criterionsignalworks/ranka/images/ranka-n1-eda-2.png

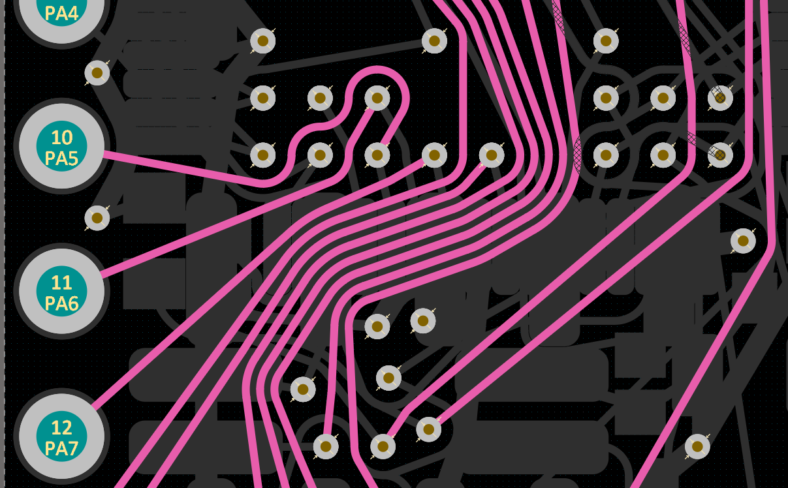
images/ranka-n1-eda-2.png
