criterionsignalworks/ranka/images/ranka-n1-eda-layer-3d.png

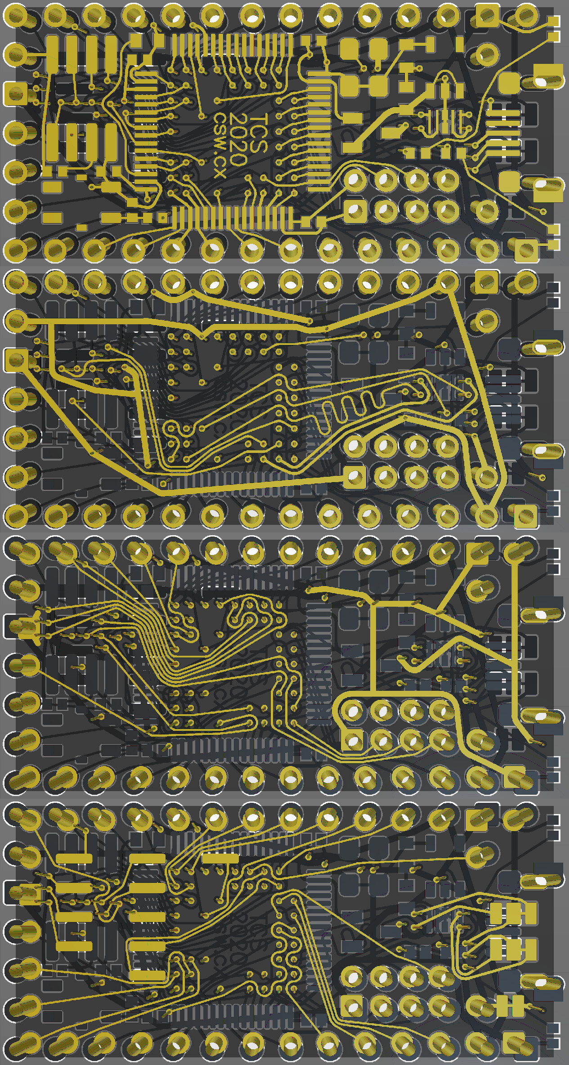
images/ranka-n1-eda-layer-3d.png
