criterionsignalworks/ranka/images/ranka-n1-top-1.jpg

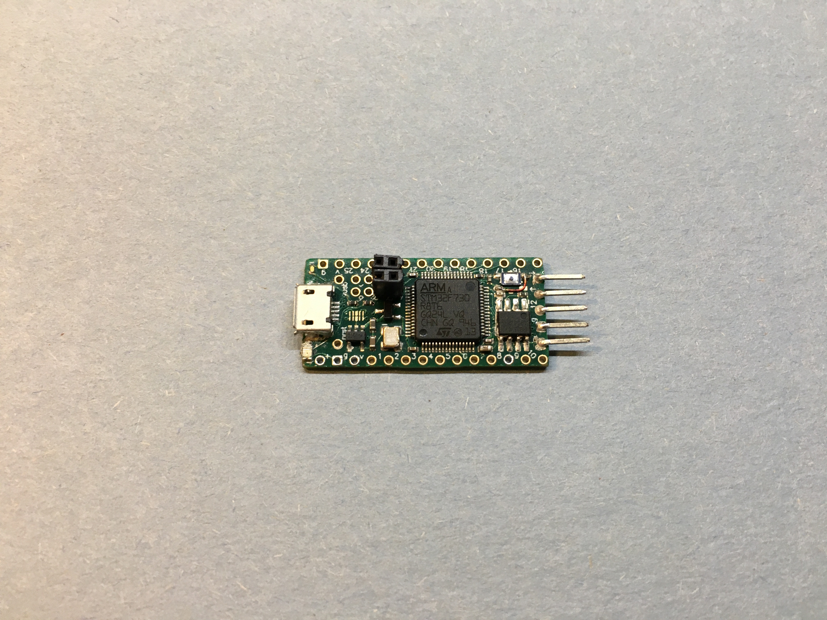
images/ranka-n1-top-1.jpg
