criterionsignalworks/ranka/images/ranka-n1-top-blurry.jpg

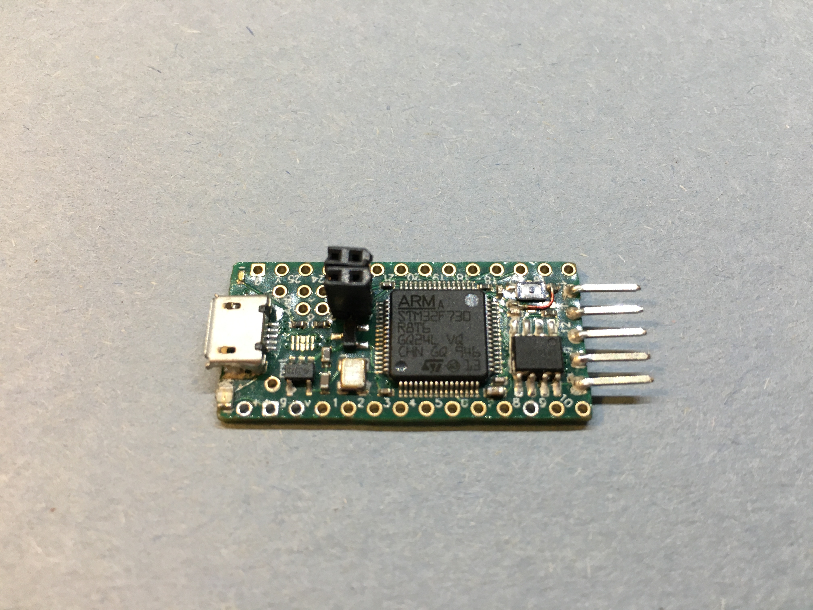
images/ranka-n1-top-blurry.jpg
