criterionsignalworks/ranka/images/tcs-ranka-n0-5.jpg

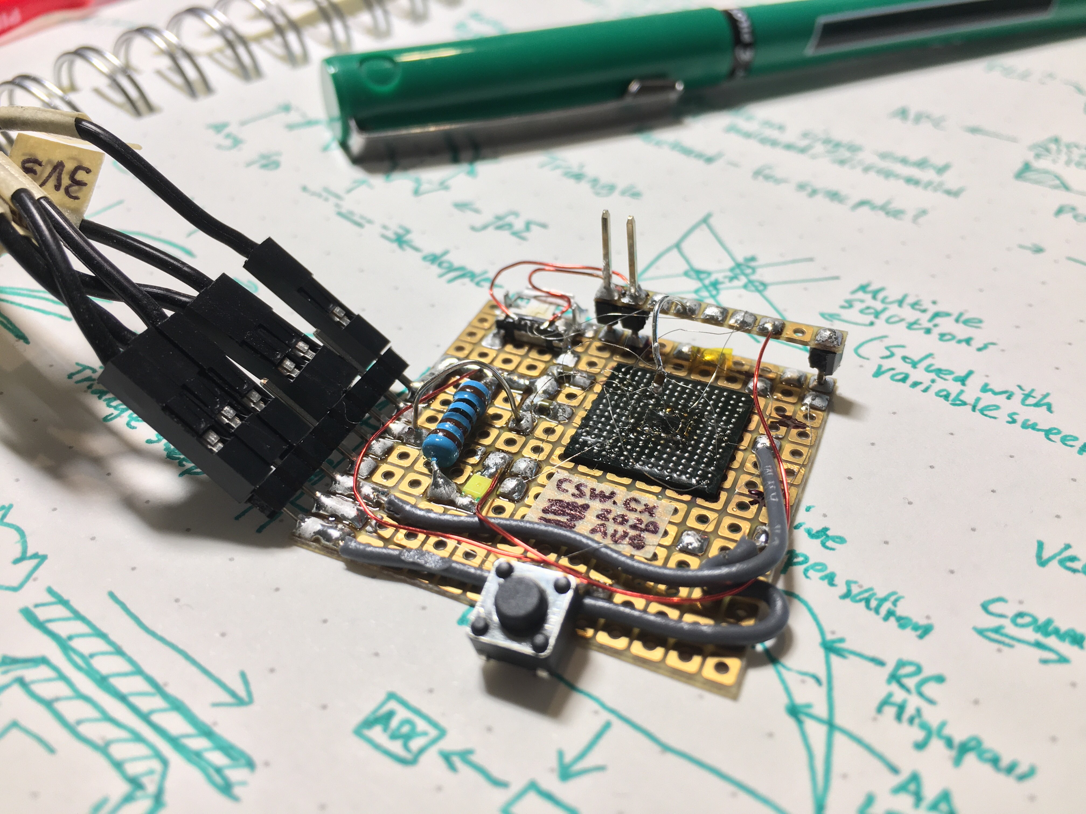
images/tcs-ranka-n0-5.jpg
